shorepine/alles/dweb2023/65xem.jpg

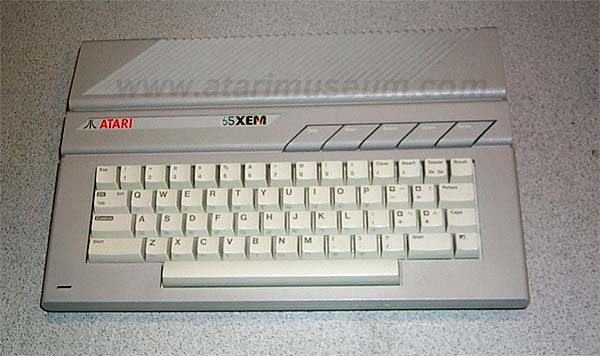
dweb2023/65xem.jpg
