shorepine/alles/dweb2023/alles-instrument-1200x900.jpg

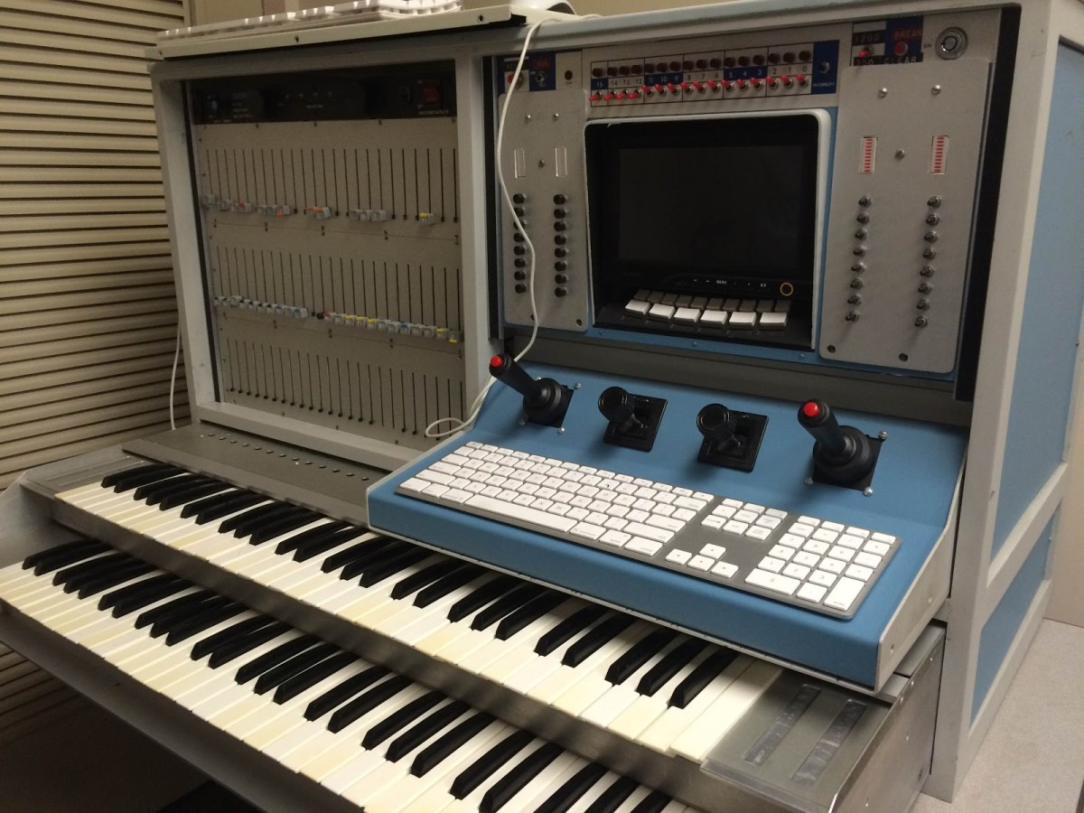
dweb2023/alles-instrument-1200x900.jpg
