shorepine/alles/dweb2023/amy.jpeg

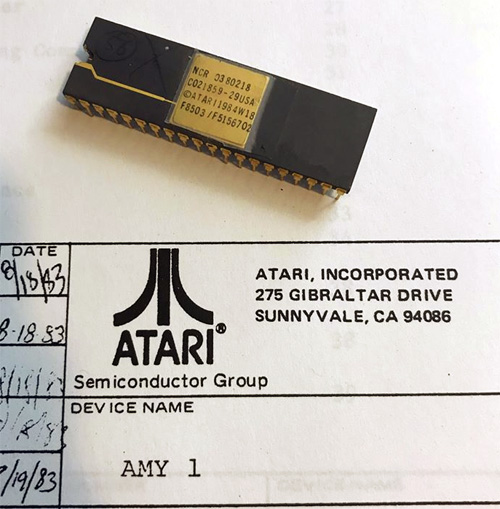
dweb2023/amy.jpeg
