shorepine/alles/pcbs/2020-11-20_alles_RevA_back.png

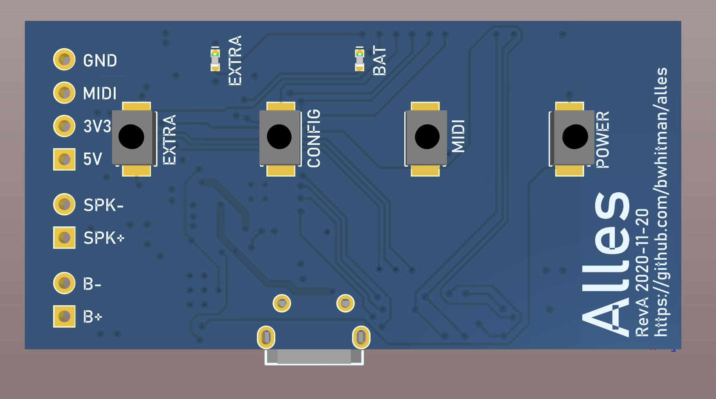
pcbs/2020-11-20_alles_RevA_back.png
