shorepine/alles/pcbs/2020-11-20_alles_RevA_front.png

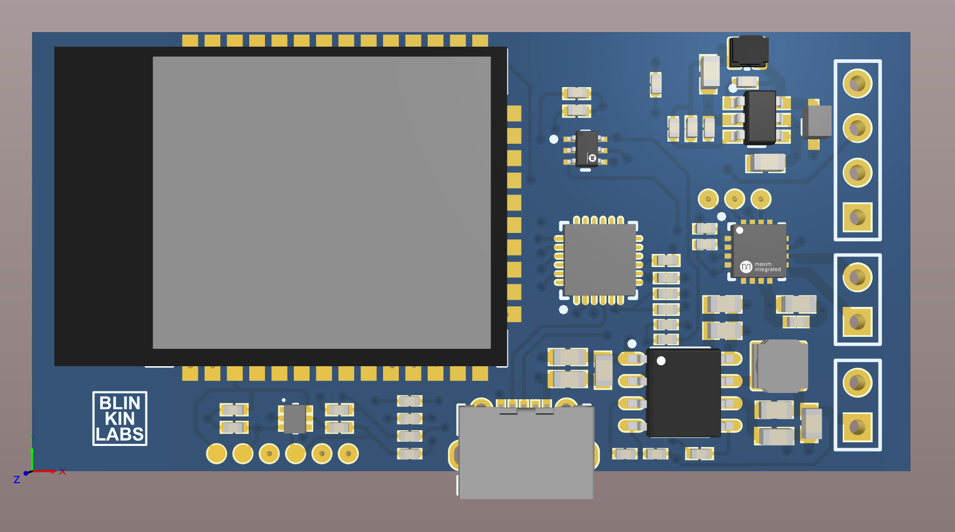
pcbs/2020-11-20_alles_RevA_front.png
