shorepine/alles/pics/alles_midi.png

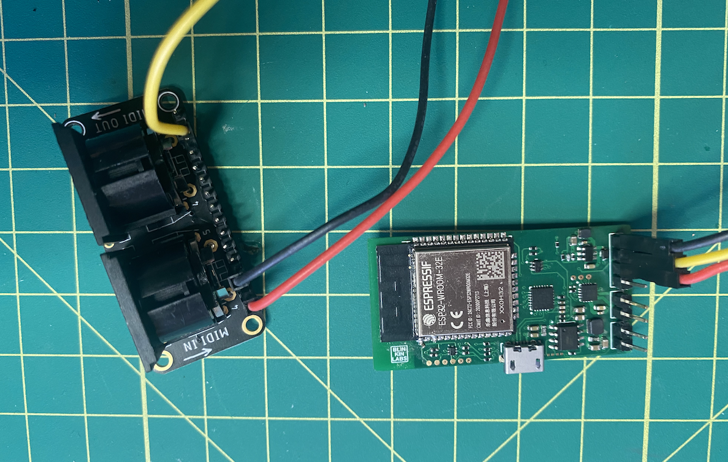
pics/alles_midi.png
