shorepine/alles/pics/closeup.png

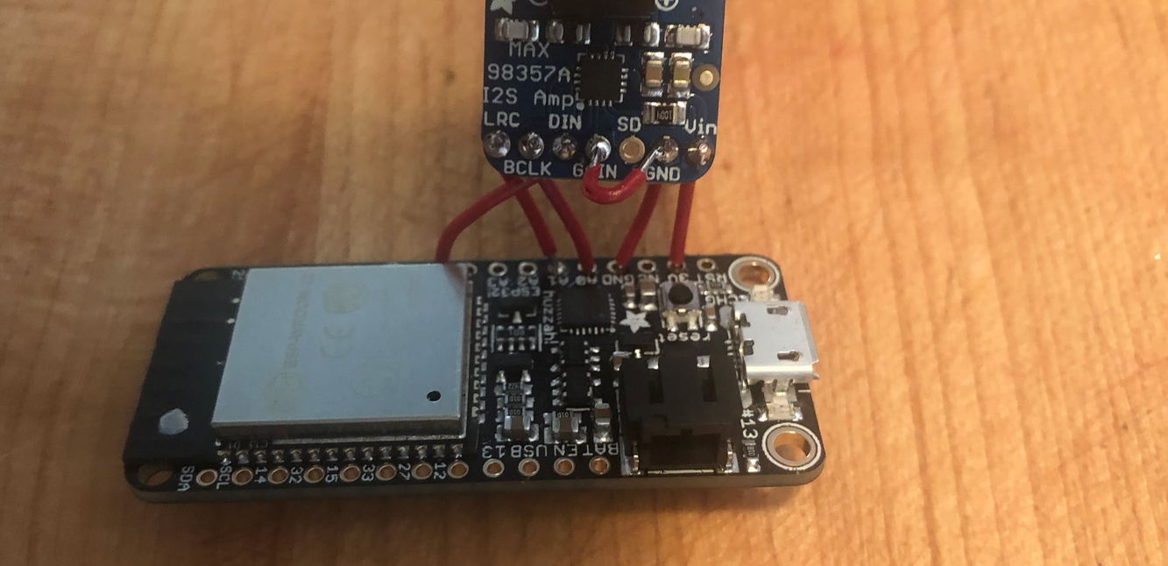
pics/closeup.png
