shorepine/alles/pics/joined.jpg

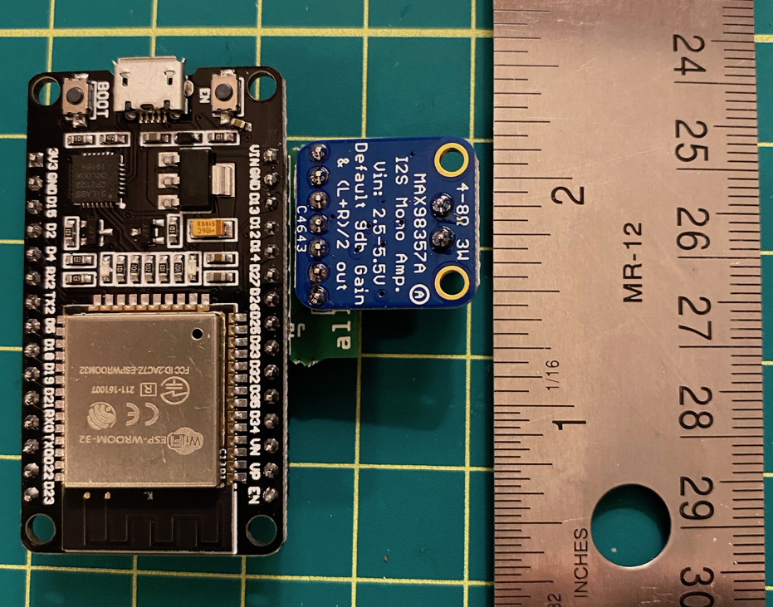
pics/joined.jpg
