shorepine/alles/pics/set.jpg

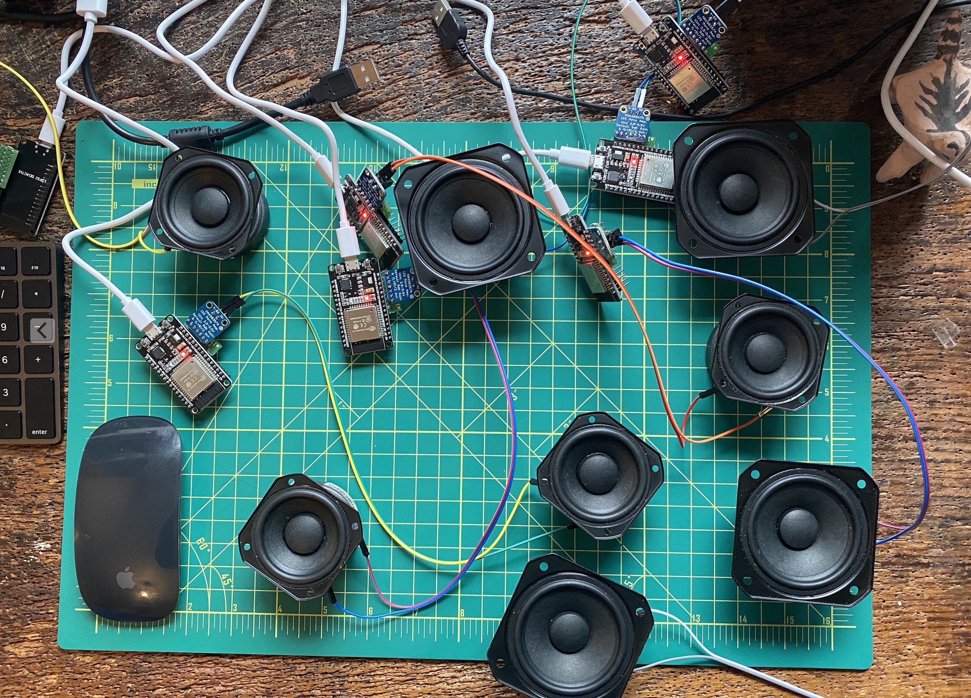
pics/set.jpg
