shorepine/alles/main/oscillators.cc

extern "C" {
#include "alles.h"
#include "sinLUT_1024.h"
#include "impulse32_1024.h"
#include "pcm.h"
}

// We only allow a couple of KS oscs as they're RAM hogs 
#define MAX_KS_BUFFER_LEN 802 // 44100/55  -- 55Hz (A1) lowest we can go for KS
#define KS_OSCS 1
float ** ks_buffer; 
uint8_t ks_polyphony_index = 0; 


extern struct event *synth;
extern struct mod_event *msynth; // the synth that is being modified by LFOs & envelopes
extern struct state global; 
//extern float *scratchbuf;



/* Dan Ellis libblosca functions */

// This is copying from Pure Data's tabread4~.
extern "C" float render_lut(float * buf, float step, float skip, float amp, const int16_t* lut, int16_t lut_size) { 
    // We assume lut_size == 2^R for some R, so (lut_size - 1) consists of R '1's in binary.
    int lut_mask = lut_size - 1;
    for(uint16_t i=0;i<BLOCK_SIZE;i++) {
        uint16_t base_index = (uint16_t)floor(step);
        float frac = step - (float)base_index;
        float b = (float)lut[(base_index + 0) & lut_mask];
        float c = (float)lut[(base_index + 1) & lut_mask];
#ifdef LINEAR_INTERP
        // linear interpolation.
        float sample = b + ((c - b) * frac);
#else /* !LINEAR_INTERP => CUBIC_INTERP */
        float a = (float)lut[(base_index - 1) & lut_mask];
        float d = (float)lut[(base_index + 2) & lut_mask];
        // cubic interpolation (TTEM p.46).
        //      float sample = 
        //    - frac * (frac - 1) * (frac - 2) / 6.0 * a
        //    + (frac + 1) * (frac - 1) * (frac - 2) / 2.0 * b
        //    - (frac + 1) * frac * (frac - 2) / 2.0 * c
        //    + (frac + 1) * frac * (frac - 1) / 6.0 * d;
        // Miller's optimization - https://github.com/pure-data/pure-data/blob/master/src/d_array.c#L440
        float cminusb = c - b;
        float sample = b + frac * (cminusb - 0.1666667f * (1.-frac) * ((d - a - 3.0f * cminusb) * frac + (d + 2.0f*a - 3.0f*b)));
#endif /* LINEAR_INTERP */
        buf[i] += sample * amp;
        step += skip;
        if(step >= lut_size) step -= lut_size;
    }
    return step;
}

extern "C" void lpf_buf(float *buf, float decay, float &state) {
    // Implement first-order low-pass (leaky integrator).
    for (uint16_t i = 0; i < BLOCK_SIZE; ++i) {
      buf[i] = decay * state + buf[i];
      state = buf[i];
    }
}

extern "C" void clear_buf(float *buf) {
    // Clear a block-sized buf.
    memset(buf, 0, BLOCK_SIZE * sizeof(float));
}

extern "C" void cumulate_buf(const float *from, float *dest) {
    for (uint16_t i = 0; i < BLOCK_SIZE; ++i) {
        dest[i] += from[i];
    }
}

/* PCM */

extern "C" void pcm_note_on(uint8_t osc) {
    // If no freq given, we set it to default PCM SR. e.g. freq=11025 plays PCM at half speed, freq=44100 double speed 
    if(synth[osc].freq <= 0) synth[osc].freq = PCM_SAMPLE_RATE;
    // If patch is given, set step directly from patch's offset
    if(synth[osc].patch>=0) {
        synth[osc].step = offset_map[synth[osc].patch*2]; // start sample
        // Use substep here as "end sample" so we don't have to add another field to the struct
        synth[osc].substep = synth[osc].step + offset_map[synth[osc].patch*2 + 1]; // end sample
    } else { // no patch # given? use phase as index into PCM buffer
        synth[osc].step = PCM_LENGTH * synth[osc].phase; // start at phase offset
        synth[osc].substep = PCM_LENGTH; // play until end of buffer and stop 
    }
}
extern "C" void pcm_lfo_trigger(uint8_t osc) {
    pcm_note_on(osc);
}

// TODO -- this just does one shot, no looping (will need extra loop parameter? what about sample metadata looping?) 
// TODO -- this should just be like render_LUT(float * buf, uint8_t osc, int16_t **LUT) as it's the same for sine & PCM?
extern "C" void render_pcm(float * buf, uint8_t osc) {
    float skip = msynth[osc].freq / (float)SAMPLE_RATE;
    for(uint16_t i=0;i<BLOCK_SIZE;i++) {
        float sample = pcm[(int)(synth[osc].step)];
        synth[osc].step = (synth[osc].step + skip);
        if(synth[osc].step >= synth[osc].substep ) { // end
            synth[osc].status=OFF;
            sample = 0;
        }
        buf[i] = buf[i] + (sample * msynth[osc].amp);
    }
}

extern "C" float compute_lfo_pcm(uint8_t osc) {
    float lfo_sr = (float)SAMPLE_RATE / (float)BLOCK_SIZE;
    float skip = msynth[osc].freq / lfo_sr;
    float sample = pcm[(int)(synth[osc].step)];
    synth[osc].step = (synth[osc].step + skip);
    if(synth[osc].step >= synth[osc].substep ) { // end
        synth[osc].status=OFF;
        sample = 0;
    }
    return (sample * msynth[osc].amp) / 16384.0; // -1 .. 1
    
}

/* Pulse wave */

extern "C" void pulse_note_on(uint8_t osc) {
    // So i reset step to some phase math, right? yeah
    synth[osc].step = (float)IMPULSE32_SIZE * synth[osc].phase;
    synth[osc].lpf_state[0] = 0;
}

extern "C" void render_pulse(float * buf, float * scratch, uint8_t osc) {
    // LPF time constant should be ~ 10x osc period, so droop is minimal.
    float period_samples = (float)SAMPLE_RATE / msynth[osc].freq;
    synth[osc].lpf_alpha = 1.0 - 1.0 / (10.0 * period_samples);
    float duty = msynth[osc].duty;
    if (duty < 0.01) duty = 0.01;
    if (duty > 0.99) duty = 0.99;
    float skip = msynth[osc].freq / (float)SAMPLE_RATE * IMPULSE32_SIZE;
    // Scale the impulse proportional to the skip so its integral remains ~constant.
    // 0.5 is to compensate for typical skip of ~2.
    float amp = msynth[osc].amp * skip * 0.1;  // was 0.5
    float pwm_step = synth[osc].step + duty * IMPULSE32_SIZE;
    if (pwm_step >= IMPULSE32_SIZE)  pwm_step -= IMPULSE32_SIZE;
    clear_buf(scratch);
    synth[osc].step = render_lut(scratch, synth[osc].step, skip, amp, impulse32, IMPULSE32_SIZE);
    render_lut(scratch, pwm_step, skip, -amp, impulse32, IMPULSE32_SIZE);
    lpf_buf(scratch, synth[osc].lpf_alpha, synth[osc].lpf_state[0]);
    // Accumulate into actual output buffer.
    cumulate_buf(scratch, buf);
}

extern "C" void pulse_lfo_trigger(uint8_t osc) {
    float lfo_sr = (float)SAMPLE_RATE / (float)BLOCK_SIZE;
    float period = 1. / (synth[osc].freq/lfo_sr);
    synth[osc].step = period * synth[osc].phase;
}

extern "C" float compute_lfo_pulse(uint8_t osc) {
    // do BW pulse gen at SR=44100/64
    float lfo_sr = (float)SAMPLE_RATE / (float)BLOCK_SIZE;
    if(msynth[osc].duty < 0.001 || msynth[osc].duty > 0.999) msynth[osc].duty = 0.5;
    float period = 1. / (msynth[osc].freq/(float)lfo_sr);
    float period2 = msynth[osc].duty * period; // if duty is 0.5, square wave
    if(synth[osc].step >= period || synth[osc].step == 0)  {
        synth[osc].sample = UP;
        synth[osc].substep = 0; // start the duty cycle counter
        synth[osc].step = 0;
    } 
    if(synth[osc].sample == UP) {
        if(synth[osc].substep++ > period2) {
            synth[osc].sample = DOWN;
        }
    }
    synth[osc].step++;
    return (synth[osc].sample * msynth[osc].amp)/16384.0; // -1 .. 1
}


/* Saw wave */

extern "C" void saw_note_on(uint8_t osc) {
    synth[osc].step = (float)IMPULSE32_SIZE * synth[osc].phase;
    synth[osc].lpf_state[0] = 0;
}

extern "C" void render_saw(float * buf, float * scratch, uint8_t osc) {
    // For saw, we *want* the lpf to droop across the period, so use a smaller alpha.
    float period_samples = (float)SAMPLE_RATE / msynth[osc].freq;
    synth[osc].lpf_alpha = 1.0 - 1.0 / period_samples;
    float skip = msynth[osc].freq / (float)SAMPLE_RATE * IMPULSE32_SIZE;
    // Scale the impulse proportional to the skip so its integral remains ~constant.
    // 0.5 is to compensate for typical skip of ~2.
    float amp = msynth[osc].amp * skip * 0.1;
    clear_buf(scratch);
    synth[osc].step = render_lut(
          scratch, synth[osc].step, skip, amp, impulse32, IMPULSE32_SIZE);
    lpf_buf(scratch, synth[osc].lpf_alpha, synth[osc].lpf_state[0]);
    cumulate_buf(scratch, buf);
}



extern "C" void saw_lfo_trigger(uint8_t osc) {
    float lfo_sr = (float)SAMPLE_RATE / (float)BLOCK_SIZE;
    float period = 1. / (synth[osc].freq/lfo_sr);
    synth[osc].step = period * synth[osc].phase;
}

extern "C" float compute_lfo_saw(uint8_t osc) {
    float lfo_sr = (float)SAMPLE_RATE / (float)BLOCK_SIZE;
    float period = 1. / (msynth[osc].freq/lfo_sr);
    if(synth[osc].step >= period || synth[osc].step == 0) {
        synth[osc].sample = DOWN;
        synth[osc].step = 0; // reset the period counter
    } else {
        synth[osc].sample = DOWN + (synth[osc].step * ((UP-DOWN) / period));
    }
    synth[osc].step++;
    return (synth[osc].sample * msynth[osc].amp)/16384.0; // -1 .. 1    
}


/* triangle wave */

extern "C" void triangle_note_on(uint8_t osc) {
    synth[osc].step = (float)IMPULSE32_SIZE * synth[osc].phase;
    synth[osc].lpf_state[0] = 0;
    synth[osc].lpf_state[1] = 0;
}

extern "C" void render_triangle(float * buf, float * scratch, uint8_t osc) {
    // Triangle has two lpfs, one to build the square, and one to integrate the pulse.
    float period_samples = (float)SAMPLE_RATE / msynth[osc].freq;
    synth[osc].lpf_alpha = 1.0 - 1.0 / (10 * period_samples);
    synth[osc].lpf_alpha_1 = 1.0 - 1.0 / period_samples;
    float duty = msynth[osc].duty;
    if (duty < 0.01) duty = 0.01;
    if (duty > 0.99) duty = 0.99;
    float skip = msynth[osc].freq / (float)SAMPLE_RATE * IMPULSE32_SIZE;
    // Scale impulses by skip to make integral independent of skip.
    // Scale by skip again so integral of each cycle of square wave is same total amp.
    // Divide by duty(1-duty) so peak integral is const regardless of duty.
    float amp = msynth[osc].amp * skip * skip / (duty - duty * duty) * 0.0001;
    float pwm_step = synth[osc].step + duty * IMPULSE32_SIZE;
    if (pwm_step >= IMPULSE32_SIZE)  pwm_step -= IMPULSE32_SIZE;
    clear_buf(scratch);
    synth[osc].step = render_lut(scratch, synth[osc].step, skip, amp, impulse32, IMPULSE32_SIZE);
    render_lut(scratch, pwm_step, skip, -amp, impulse32, IMPULSE32_SIZE);
    // Integrate once to get square wave.
    lpf_buf(scratch, synth[osc].lpf_alpha, synth[osc].lpf_state[0]);
    // Integrate again to get triangle wave.
    lpf_buf(scratch, synth[osc].lpf_alpha_1, synth[osc].lpf_state[1]);
    cumulate_buf(scratch, buf);
}


extern "C" void triangle_lfo_trigger(uint8_t osc) {
    float lfo_sr = (float)SAMPLE_RATE / (float)BLOCK_SIZE;
    float period = 1. / (synth[osc].freq/lfo_sr);
    synth[osc].step = period * synth[osc].phase;
}

extern "C" float compute_lfo_triangle(uint8_t osc) {
    float lfo_sr = (float)SAMPLE_RATE / (float)BLOCK_SIZE;    
    float period = 1. / (msynth[osc].freq/lfo_sr);
    if(synth[osc].step >= period || synth[osc].step == 0) {
        synth[osc].sample = DOWN;
        synth[osc].step = 0; // reset the period counter
    } else {
        if(synth[osc].step < (period/2.0)) {
            synth[osc].sample = DOWN + (synth[osc].step * ((UP-DOWN) / period * 2));
        } else {
            synth[osc].sample = UP - ((synth[osc].step-(period/2)) * ((UP-DOWN) / period * 2));
        }
    }
    synth[osc].step++;
    return (synth[osc].sample * msynth[osc].amp) / 16384.0; // -1 .. 1
    
}

/* sine */

extern "C" void sine_note_on(uint8_t osc) {
    synth[osc].step = (float)SINLUT_SIZE * synth[osc].phase;
}

extern "C" void render_sine(float * buf, uint8_t osc) { 
    float skip = msynth[osc].freq / (float)SAMPLE_RATE * SINLUT_SIZE;
    synth[osc].step = render_lut(buf, synth[osc].step, skip, msynth[osc].amp, sinLUT, SINLUT_SIZE);
}

extern "C" float compute_lfo_sine(uint8_t osc) { 
    float lfo_sr = (float)SAMPLE_RATE / (float)BLOCK_SIZE;
    float skip = msynth[osc].freq / lfo_sr * SINLUT_SIZE;

    int lut_mask = SINLUT_SIZE - 1;
    uint16_t base_index = (uint16_t)floor(synth[osc].step);
    float frac = synth[osc].step - (float)base_index;
    float b = (float)sinLUT[(base_index + 0) & lut_mask];
    float c = (float)sinLUT[(base_index + 1) & lut_mask];
    // linear interpolation for the LFO 
    float sample = b + ((c - b) * frac);
    synth[osc].step += skip;
    if(synth[osc].step >= SINLUT_SIZE) synth[osc].step -= SINLUT_SIZE;
    return (sample * msynth[osc].amp)/16384.0; // -1 .. 1
}


extern "C" void sine_lfo_trigger(uint8_t osc) {
    sine_note_on(osc);
}

/* noise */

extern "C" void render_noise(float *buf, uint8_t osc) {
    for(uint16_t i=0;i<BLOCK_SIZE;i++) {
        buf[i] = buf[i] + ( (int16_t) ((esp_random() >> 16) - 32768) * msynth[osc].amp);
    }
}

extern "C" float compute_lfo_noise(uint8_t osc) {
    return ( (int16_t) ((esp_random() >> 16) - 32768) * msynth[osc].amp) / 16384.0; // -1..1
}

/* karplus-strong */

extern "C" void render_ks(float * buf, uint8_t osc) {
    if(msynth[osc].freq >= 55) { // lowest note we can play
        uint16_t buflen = floor(SAMPLE_RATE / msynth[osc].freq);
        for(uint16_t i=0;i<BLOCK_SIZE;i++) {
            uint16_t index = floor(synth[osc].step);
            synth[osc].sample = ks_buffer[ks_polyphony_index][index];
            ks_buffer[ks_polyphony_index][index] = (ks_buffer[ks_polyphony_index][index] + ks_buffer[ks_polyphony_index][(index + 1) % buflen]) * 0.5 * synth[osc].feedback;
            synth[osc].step = (index + 1) % buflen;
            buf[i] = buf[i] + synth[osc].sample * msynth[osc].amp;
        }
    }
}

extern "C" void ks_note_on(uint8_t osc) {
    if(msynth[osc].freq<=0) msynth[osc].freq = 1;
    uint16_t buflen = floor(SAMPLE_RATE / msynth[osc].freq);
    if(buflen > MAX_KS_BUFFER_LEN) buflen = MAX_KS_BUFFER_LEN;
    // init KS buffer with noise up to max
    for(uint16_t i=0;i<buflen;i++) {
        ks_buffer[ks_polyphony_index][i] = ( (int16_t) ((esp_random() >> 16) - 32768) );
    }
    ks_polyphony_index++;
    if(ks_polyphony_index == KS_OSCS) ks_polyphony_index = 0;
}

extern "C" void ks_note_off(uint8_t osc) {
    msynth[osc].amp = 0;
}


extern "C" void ks_init(void) {
    // 6ms buffer
    ks_buffer = (float**) malloc(sizeof(float*)*KS_OSCS);
    for(int i=0;i<KS_OSCS;i++) ks_buffer[i] = (float*)malloc(sizeof(float)*MAX_KS_BUFFER_LEN); 
}

extern "C" void ks_deinit(void) {
    for(int i=0;i<KS_OSCS;i++) free(ks_buffer[i]);
    free(ks_buffer);
}
