shorepine/alles/main/alles.h

// alles.h
#ifndef __ALLES_H
#define __ALLES_H

#include <stdio.h>
#include <stddef.h>
#ifdef ESP_PLATFORM
#include "freertos/FreeRTOS.h"
#include "freertos/task.h"
#include "freertos/queue.h"
#include "freertos/event_groups.h"

#include "esp_system.h"
#include "esp_intr_alloc.h"
#include "esp_attr.h"
#include "esp_event.h"
#include "esp_log.h"
#include "esp_err.h"
#include "nvs_flash.h"
#include "lwip/netdb.h"
#include "wifi_manager.h"
#include "driver/gpio.h"


#define MAX_TASKS 8

// Pins & buttons
#define BUTTON_WAKEUP 34
#define BUTTON_MINUS 17
#define BUTTON_WIFI 16
#define BUTTON_PLUS 0
#define ESP_INTR_FLAG_DEFAULT 0
#define CONFIG_I2S_LRCLK 25
#define CONFIG_I2S_BCLK 26
#define CONFIG_I2S_DIN 27
#define CONFIG_I2S_NUM 0 
#define BAT_SENSE_EN 32
#define CHARGE_STAT 33
#define POWER_5V_EN 21
#define BATT_SENSE_CHANNEL ADC_CHANNEL_7 // GPIO35 / ADC1_7
#define WALL_SENSE_CHANNEL ADC_CHANNEL_3 // GPIO39 / ADC1_3
#define CPU_MONITOR_0 13
#define CPU_MONITOR_1 12
#define CPU_MONITOR_2 15

void wifi_reconfigure();
extern esp_err_t buttons_init();
void esp_show_debug(uint8_t type);
void delay_ms(uint32_t ms);

#endif


// Choose to use big pcm patches bank or small -- depends on platform, but both Alles v2 and local can support large. Tulip can't 
#define ALLES_LATENCY_MS 1000 // fixed default latency in milliseconds, can change
#include "amy.h"

#define UDP_PORT 9294        // port to listen on
#define MULTICAST_TTL 255     // hops multicast packets can take
#define MULTICAST_IPV4_ADDR "232.10.11.12"
#define PING_TIME_MS 10000   // ms between boards pinging each other
#define MAX_RECEIVE_LEN 4096

// enums
#define DEVBOARD 0
#define ALLES_BOARD_V1 1
#define ALLES_BOARD_V2 2
#define ALLES_DESKTOP 3
#define BATTERY_STATE_CHARGING 0x01
#define BATTERY_STATE_CHARGED 0x02
#define BATTERY_STATE_DISCHARGING 0x04
#define BATTERY_VOLTAGE_4 0x10
#define BATTERY_VOLTAGE_3 0x20
#define BATTERY_VOLTAGE_2 0x40
#define BATTERY_VOLTAGE_1 0x80

#define ALLES_MAX_DRIFT_MS 20000


// Status mask 
#define RUNNING 1
#define WIFI_MANAGER_OK 2
#define UPDATE 4

extern char *message_start_pointer;
extern int16_t message_length;

extern void bleep(uint32_t start);
extern void debleep();
extern void upgrade_tone();
extern void wifi_tone();
extern void scale(uint8_t wave);

extern uint8_t alive;
extern int16_t client_id;

void ping(int64_t sysclock);
amy_err_t sync_init();

extern  void update_map(int16_t client, uint8_t ipv4, int64_t time);
extern void handle_sync(int64_t time, int8_t index);
extern void mcast_send(char * message, uint16_t len);
#ifndef ESP_PLATFORM
extern void *mcast_listen_task(void *vargp);
#endif
extern void create_multicast_ipv4_socket();
void alles_parse_message(char *message, uint16_t length);





#endif
