shorepine/alles/main/sounds.c

// sounds.c
// various little "make a sound in firmware" methods
#include "alles.h"

void note_on(int8_t osc, int64_t time) {
    struct event e = amy_default_event();
    e.osc = osc;
    e.time = time;
    e.velocity = 1;
    amy_add_event(e);
}


// Play a pew -- upgdrading

void upgrade_tone() {
    struct event e = amy_default_event();
    int64_t sysclock = amy_sysclock();
    e.osc = 0;
    e.time = sysclock;
    e.wave = SINE;
    e.freq_coefs[COEF_CONST] = 220;
    strcpy(e.bp0, "0,0,10,1,500,0,0,0");
    amy_add_event(e);
    e.osc = 1;
    e.freq_coefs[COEF_CONST] = 420;
    amy_add_event(e);

    note_on(0, e.time+1);
    note_on(1, e.time+1);
}

// Play a sonar ping -- searching for wifi
void wifi_tone() {
    struct event e = amy_default_event();
    int64_t sysclock = amy_sysclock();
    e.osc = 0;
    e.time = sysclock;
    e.wave = SINE;
    e.freq_coefs[COEF_CONST] = 440;
    strcpy(e.bp0 ,"0,1,10,1,500,0,0,0");
    amy_add_event(e);
    e.osc = 1;
    e.freq_coefs[COEF_CONST] = 840;
    amy_add_event(e);

    note_on(0, e.time+1);
    note_on(1, e.time+1);
}


// Schedule a bleep now
void bleep(uint32_t start) {
    struct event e = amy_default_event();
    int64_t sysclock = amy_sysclock();
    e.osc = 0;
    e.time = start;
    e.wave = SINE;
    e.freq_coefs[COEF_CONST] = 220;
    amy_add_event(e);
    e.velocity = 1;
    e.pan_coefs[COEF_CONST] = 0.9;
    amy_add_event(e);
    e.time = sysclock + 150;
    e.freq_coefs[COEF_CONST] = 440;
    e.pan_coefs[COEF_CONST] = 0.1;
    amy_add_event(e);
    e.time = sysclock + 300;
    e.velocity = 0;
    e.pan_coefs[COEF_CONST] = 0.5;  // Restore default pan to osc 0.
    amy_add_event(e);
}

void debleep() {
    struct event e = amy_default_event();
    int64_t sysclock = amy_sysclock();
    e.time = sysclock;
    e.wave = SINE;
    e.freq_coefs[COEF_CONST] = 440;
    e.velocity = 1;
    amy_add_event(e);
    e.time = sysclock + 150;
    e.freq_coefs[COEF_CONST] = 220;
    amy_add_event(e);
    e.time = sysclock + 300;
    e.velocity = 0;
    e.freq_coefs[COEF_CONST] = 0;
    amy_add_event(e);
}
